bergamifer/domosonica/render/Modulo-completo.jpg

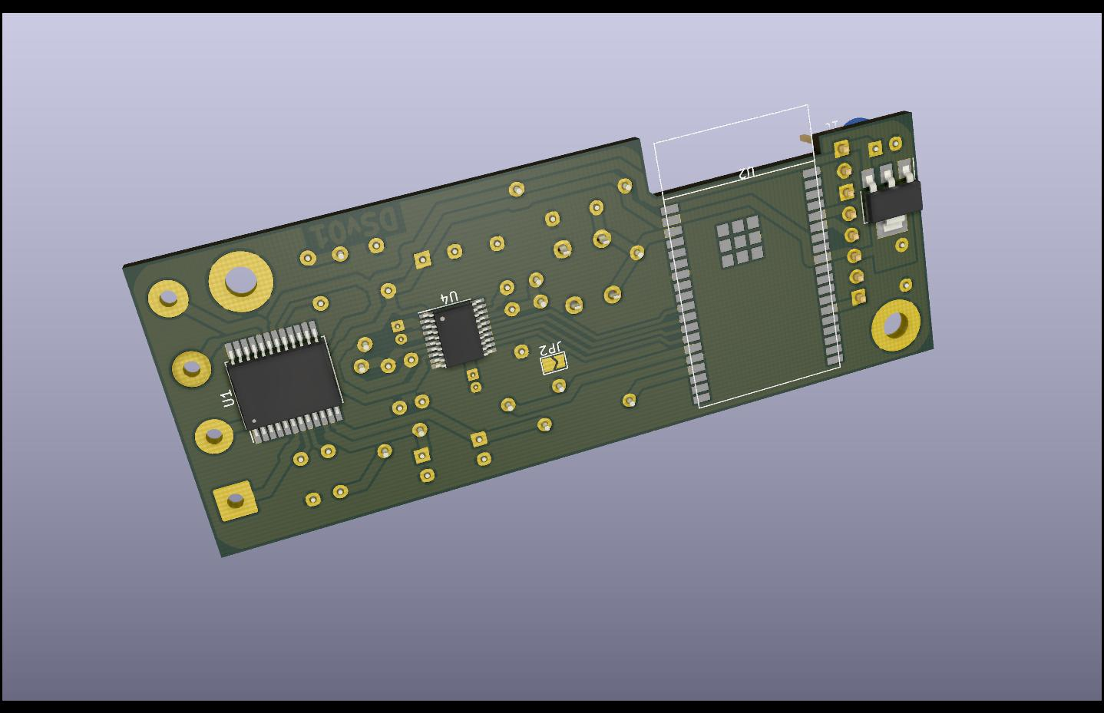
render/Modulo-completo.jpg
