bergamifer/domosonica/render/Modulo-completo.png

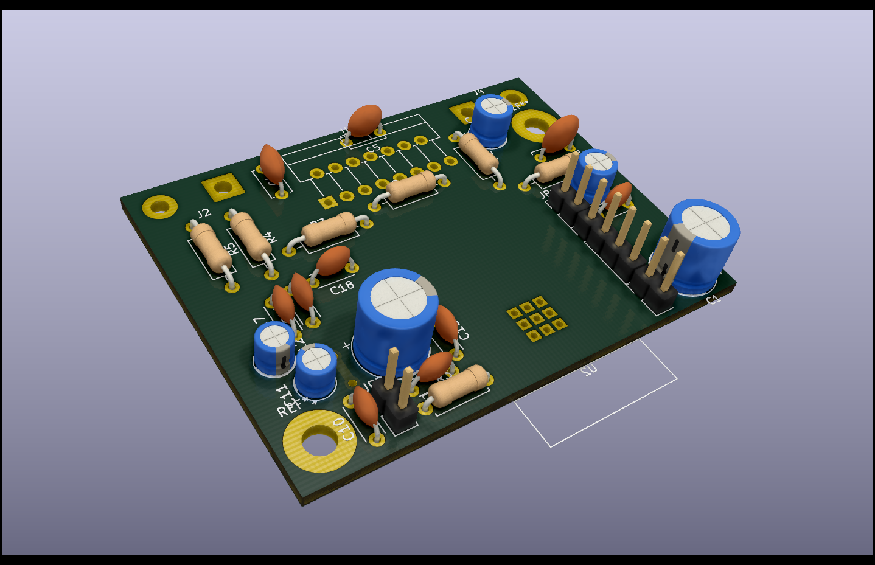
render/Modulo-completo.png
